oskitone/scout/openscad/keys.scad

/* TODO: extract into common parts repo */
use <../../poly555/openscad/lib/keys.scad>;
use <../../poly555/openscad/lib/utils.scad>;

include <nuts_and_bolts.scad>;
include <utils.scad>;

KEYS_COUNT = 17;
KEYS_MOUNT_LENGTH = NUT_DIAMETER;
KEYS_FRONT_BOTTOM_CHAMFER = 1;

function get_key_to_pcb_x_offset(
    key_width,
    key_gutter
) = ((key_width - BUTTON_DIAMETER) / 2 - key_gutter);

function get_keys_full_width(
    key_width,
    key_gutter
) = (
    let (natural_key_count = get_natural_key_count(KEYS_COUNT, 0))
    natural_key_count * key_width + (natural_key_count - 1) * key_gutter
);

function get_keys_to_enclosure_distance(
    tolerance = 0,
    key_gutter
) = (
    key_gutter - tolerance * 2
);

function get_keys_mount_rail_width(
    tolerance,
    key_width,
    key_gutter
) = (
    get_keys_full_width(key_width, key_gutter)
    + get_keys_to_enclosure_distance(tolerance, key_gutter) * 2
);

module keys_mount_alignment_fixture(
    height,
    cavity,
    key_width,
    key_gutter,
    tolerance = 0,

    fixture_width = 1,
    fixture_length = 2
) {
    e = .0825;

    x_bleed = cavity ? 0 : tolerance + e;
    z_bleed = cavity ? e : 0;

    fixture_width = cavity
        ? fixture_width + tolerance
        : fixture_width + x_bleed - tolerance;
    fixture_length = cavity
        ? fixture_length + tolerance
        : fixture_length - tolerance * 2;

    xs = [
        -e - x_bleed,
        get_keys_mount_rail_width(tolerance, key_width, key_gutter)
            - fixture_width + x_bleed
    ];

    for (x = xs) {
        y = (KEYS_MOUNT_LENGTH - fixture_length) / 2;
        translate([x, y, -z_bleed]) {
            cube([fixture_width + e, fixture_length, height + z_bleed * 2]);
        }
    }
}

module keys_mount_rail(
    height,
    key_width,
    key_length,
    key_gutter,
    front_y_bleed = 0,
    include_alignment_fixture = true,
    pcb_screw_hole_positions = [],
    tolerance = 0
) {
    keys_to_enclosure_distance =
        get_keys_to_enclosure_distance(tolerance, key_gutter);

    translate([-keys_to_enclosure_distance, key_length - front_y_bleed, 0]) {
        difference() {
            cube([
                get_keys_mount_rail_width(tolerance, key_width, key_gutter),
                KEYS_MOUNT_LENGTH + front_y_bleed,
                height
            ]);

            translate([
                get_key_to_pcb_x_offset(key_width, key_gutter)
                    + keys_to_enclosure_distance,
                KEYS_MOUNT_LENGTH / 2 + front_y_bleed,
                0
            ]) {
                scout_pcb_holes(
                    y = 0,
                    height = height,
                    positions = pcb_screw_hole_positions,
                    include_relief_holes = false
                );
            }

            if (include_alignment_fixture) {
                translate([0, front_y_bleed, 0]) {
                    keys_mount_alignment_fixture(
                        height = height,
                        key_width = key_width,
                        key_gutter = key_gutter,
                        cavity = true,
                        tolerance = tolerance
                    );
                }
            }
        }
    }
}

module keys(
    key_height = 7,
    accidental_height = 0,
    tolerance = 0,

    cantilever_length = 0,
    cantilever_height = 0,
    cantilver_mount_height = 0,
    nut_lock_floor = 0,

    keys_count = KEYS_COUNT,
    starting_natural_key_index = 0,

    keys_position = [],
    pcb_position = [],
    pcb_screw_hole_positions = [],

    keys_cavity_height_z,
    key_width,
    key_length,
    travel = 0,
    key_gutter,

    front_bottom_chamfer = KEYS_FRONT_BOTTOM_CHAMFER,

    accidental_color = "#444",
    natural_color = "#fff",
    natural_color_cavity = "#eee",

    quick_preview = true,
    show_clearance = false
) {
    e = .0234;

    keys_full_width = get_keys_full_width(key_width, key_gutter);

    module _keys(
        include_natural = false,
        include_accidental = false,
        include_cantilevers = false
    ) {
        mounted_keys(
            count = keys_count,
            starting_natural_key_index = starting_natural_key_index,

            natural_length = key_length,
            natural_width = key_width,
            natural_height = key_height,

            accidental_width = PCB_KEY_PLOT * 2 * .5,
            accidental_length = key_length * 3/5,
            accidental_height = key_height + accidental_height,

            front_fillet = quick_preview ? 0 : 1.5,
            sides_fillet = quick_preview ? 0 : 1,

            gutter = key_gutter,

            include_mount = false,
            include_natural = include_natural,
            include_accidental = include_accidental,
            include_cantilevers = include_cantilevers,

            cantilever_length = cantilever_length,
            cantilever_height = cantilever_height,
            cantilever_recession = cantilever_length
        );
    }

    difference() {
        union() {
            e_translate(keys_position, [0, 1, -1]) {
                color(accidental_color) {
                    _keys(
                        include_natural = false,
                        include_accidental = true,
                        include_cantilevers = true
                    );
                }
            }

            color(natural_color) {
                translate(keys_position) {
                    _keys(
                        include_natural = true,
                        include_accidental = false,
                        include_cantilevers = true
                    );

                    keys_mount_rail(
                        height = cantilver_mount_height,
                        key_width = key_width,
                        key_length = key_length,
                        key_gutter = key_gutter,
                        front_y_bleed = e,
                        pcb_screw_hole_positions = pcb_screw_hole_positions,
                        tolerance = tolerance
                    );
                }
            }
        }

        color(natural_color_cavity) {
            key_lip_endstop(
                keys_cavity_height_z,
                keys_full_width = keys_full_width,
                distance_into_keys_bleed = tolerance * 4,
                travel = travel,
                key_gutter = key_gutter
            );

            if (front_bottom_chamfer > 0) {
                translate([
                    keys_position.x - e,
                    keys_position.y - e,
                    keys_position.z - e
                ]) {
                    flat_top_rectangular_pyramid(
                        top_width = keys_full_width + e * 2,
                        top_length = 0,
                        bottom_width = keys_full_width + e * 2,
                        bottom_length = front_bottom_chamfer,
                        height = front_bottom_chamfer,
                        top_weight_y = 0
                    );
                }
            }
        }
    }

    if (show_clearance) {
        translate([
            keys_position.x,
            keys_position.y,
            keys_position.z - travel
        ]) {
            % flat_top_rectangular_pyramid(
                top_width = keys_full_width,
                top_length = key_length + e,
                bottom_width = keys_full_width,
                bottom_length = 0,
                height = travel + e,
                top_weight_y = 0
            );
        }
    }
}
