oskitone/scout/openscad/switch_clutch.scad

/* TODO: extract into common parts repo */
use <../../apc/openscad/rib_cavities.scad>;

include <enclosure.scad>;
include <switch.scad>;

ACCESSORY_FILLET = 1;
DEFAULT_TOLERANCE = .1;

SWITCH_CLUTCH_GRIP_LENGTH = 10;
SWITCH_CLUTCH_GRIP_HEIGHT = 7;

function get_switch_clutch_length_with_travel(web_length_extension) = (
    SWITCH_CLUTCH_GRIP_LENGTH + SWITCH_ACTUATOR_TRAVEL
    + web_length_extension * 2
);

module switch_clutch(
    position = 0,

    web_available_width = 2,
    web_length_extension = 1,

    enclosure_height = 0,
    vertical_clearance = DEFAULT_DFM_LAYER_HEIGHT,

    x_clearance = .2,

    grip_length = SWITCH_CLUTCH_GRIP_LENGTH,
    grip_height = SWITCH_CLUTCH_GRIP_HEIGHT,

    fillet = ACCESSORY_FILLET,
    chamfer = .6,
    side_overexposure = ENCLOSURE_SIDE_OVEREXPOSURE,
    tolerance = DEFAULT_TOLERANCE,

    outer_color = undef,
    cavity_color = undef,

    show_dfm = false,
    quick_preview = true
) {
    e = .0592;

    web_height_extension = (
        enclosure_height
        - grip_height
        - vertical_clearance * 2
        - ENCLOSURE_FLOOR_CEILING * 2
    ) / 2;
    web_x_gap = tolerance * 2 + x_clearance;
    web_width = web_available_width - web_x_gap * 2;
    web_length = SWITCH_CLUTCH_GRIP_LENGTH + web_length_extension * 2;
    web_height = grip_height + web_height_extension * 2;

    exposed_grip_width = ENCLOSURE_WALL + side_overexposure
        + (web_available_width - web_width);

    dfm_support_x = -web_width - exposed_grip_width + fillet;
    dfm_support_y = (web_length - grip_length) / 2;

    module _exposed_grip() {
        x = -web_width - exposed_grip_width;
        y = (web_length - grip_length) / 2;

        translate([x, y, web_height_extension]) {
            difference() {
                color(outer_color) {
                    rounded_cube(
                        [
                            exposed_grip_width + fillet + e,
                            grip_length,
                            grip_height
                        ],
                        quick_preview ? 0 : fillet,
                        $fn = LOFI_ROUNDING
                    );
                }

                color(cavity_color) {
                    rib_cavities(
                        length = grip_length,
                        height = grip_height
                    );
                }
            }
        }
    }

    module _web() {
        module _end(bottom) {
            connecting_width = web_width - tolerance;
            connecting_length = web_length;

            end_width = connecting_width - chamfer * 2;
            end_length = connecting_length - chamfer * 2;

            position = bottom
                ? [-web_width + chamfer, chamfer, 0]
                : [-web_width, 0, web_height - chamfer];

            translate(position) {
                flat_top_rectangular_pyramid(
                    top_width = bottom ? connecting_width : end_width,
                    top_length = bottom ? connecting_length : end_length,
                    bottom_width = bottom ? end_width : connecting_width,
                    bottom_length = bottom ? end_length : connecting_length,
                    height = chamfer
                );
            }
        }

        _end(bottom = true);
        translate([-web_width, 0, chamfer - e]) {
            cube([
                web_width - tolerance,
                web_length,
                web_height - chamfer * 2 + e
            ]);
        }
        _end(bottom = false);
    }

    module _actuator_cavity() {
        width = SWITCH_ACTUATOR_WIDTH - web_x_gap + tolerance;
        length = SWITCH_ACTUATOR_LENGTH + tolerance * 2;

        translate([-width, (web_length - length) / 2, -e]) {
            cube([width + e, length, web_height + e * 2]);
        }
    }

    module _dfm_support(brim_depth = 1) {
        height = web_height_extension - DEFAULT_DFM_LAYER_HEIGHT;

        translate([dfm_support_x, dfm_support_y, 0]) {
            cube([BREAKAWAY_SUPPORT_DEPTH, grip_length, height]);

            translate([-brim_depth, -brim_depth, 0]) {
                cube([
                    BREAKAWAY_SUPPORT_DEPTH + brim_depth * 2,
                    grip_length + brim_depth * 2,
                    DEFAULT_DFM_LAYER_HEIGHT
                ]);
            }
        }
    }

    module _dfm_cavity() {
        x = dfm_support_x + BREAKAWAY_SUPPORT_DEPTH;
        y = dfm_support_y + BREAKAWAY_SUPPORT_DEPTH + fillet;
        z = web_height_extension;

        width = exposed_grip_width - fillet - BREAKAWAY_SUPPORT_DEPTH + e;
        length = grip_length - BREAKAWAY_SUPPORT_DEPTH * 2 - fillet * 2;

        translate([x, y, z - e]) {
            cube([width, length, DEFAULT_DFM_LAYER_HEIGHT + e]);
        }
    }

    translate([
        -SWITCH_ORIGIN.x - web_x_gap,
        -SWITCH_ORIGIN.y
            + SWITCH_BASE_LENGTH / 2
            - grip_length / 2
            + SWITCH_ACTUATOR_TRAVEL / 2
            - (1 - position) * SWITCH_ACTUATOR_TRAVEL
            - web_length_extension,
        ENCLOSURE_FLOOR_CEILING + vertical_clearance
    ]) {
        difference() {
            union() {
                _exposed_grip();

                color(outer_color) {
                    _web();

                    if (show_dfm) {
                        _dfm_support();
                    }
                }
            }

            color(cavity_color) {
                _actuator_cavity();
            }

            if (show_dfm) {
                _dfm_cavity();
            }
        }
    }
}

* group() {
switch_clutch(abs($t - .5) * 2);
% switch(abs($t - .5) * 2);
}
